HACKCLUBGANG/OledWEsp/Schematic/butterflyhairclip.kicad_sch

## KiCad design Schematic/butterflyhairclip.kicad_sch (2026-09-25)

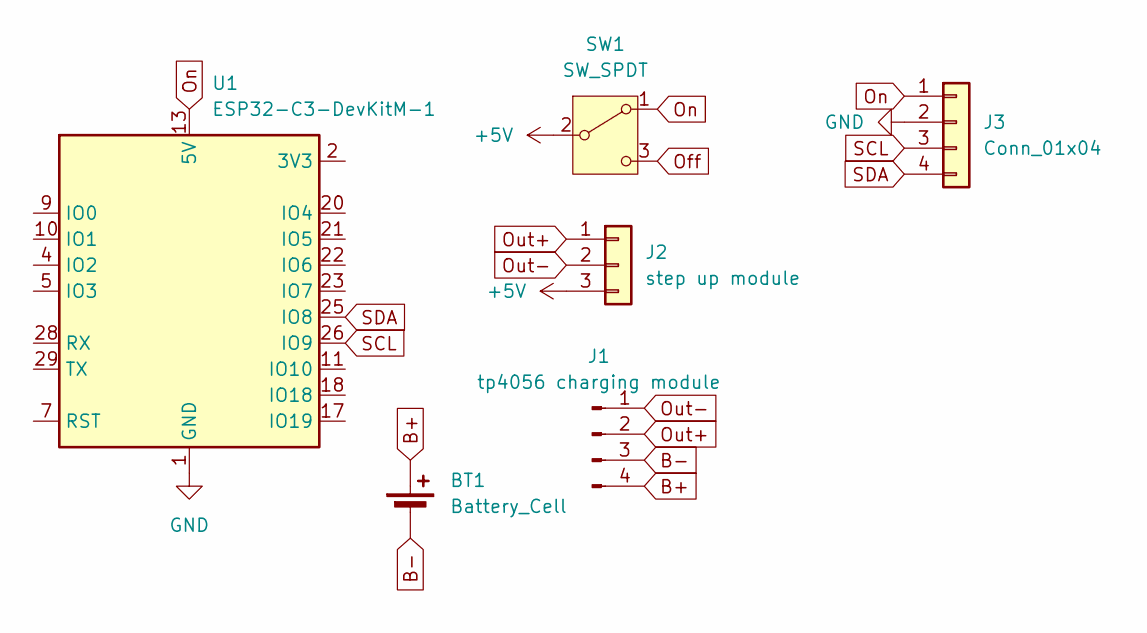
[picture p3: schematic butterflyhairclip.kicad_sch]

Parts:
BT1: Battery_Cell
J1: tp4056 charging module
J2: step up module
J3: Conn_01x04
SW1: SW_SPDT
U1: ESP32-C3-DevKitM-1

Connections:
+5V: J2.3, SW1.2 (B)
B+: BT1.1 (+), J1.4
B-: BT1.2 (-), J1.3
GND: J3.2, U1.1 (GND), U1.6 (GND), U1.8 (GND), U1.12 (GND), U1.15 (GND), U1.16 (GND), U1.19 (GND), U1.24 (GND), U1.27 (GND), U1.30 (GND)
unnamed: U1.2 (3V3), U1.3 (3V3)
Off: SW1.3 (C)
On: J3.1, SW1.1 (A), U1.13 (5V), U1.14 (5V)
Out+: J1.2, J2.1
Out-: J1.1, J2.2
SCL: J3.3, U1.26 (IO9)
SDA: J3.4, U1.25 (IO8)
